Hazzd12/dissertation_2024/docs/asset/sensor_box.jpg

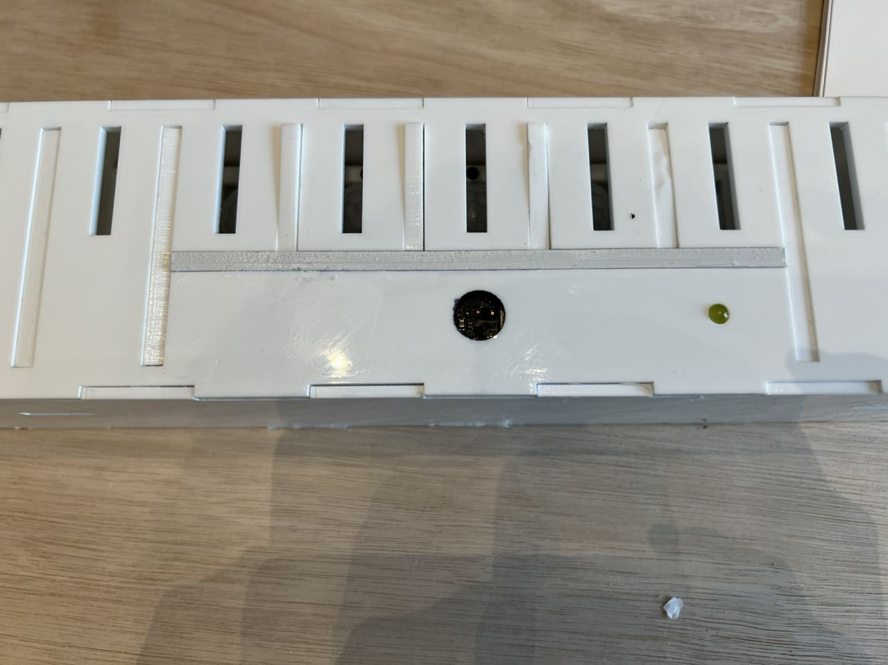
docs/asset/sensor_box.jpg
