Hazzd12/dissertation_2024/docs/asset/sensor_hole.jpg

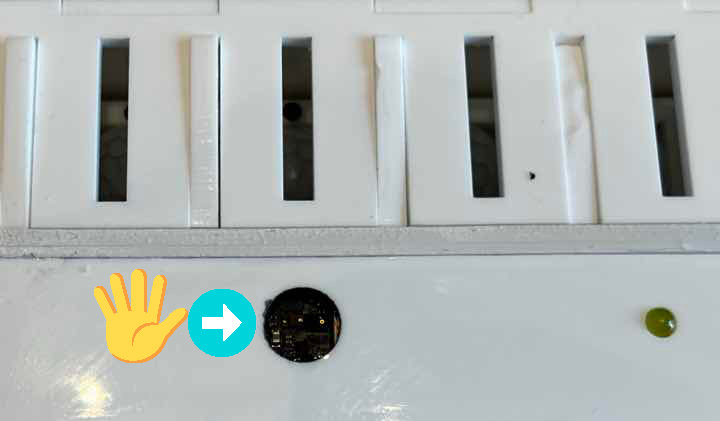
docs/asset/sensor_hole.jpg
