Hazzd12/dissertation_2024/dxf/sensor.png

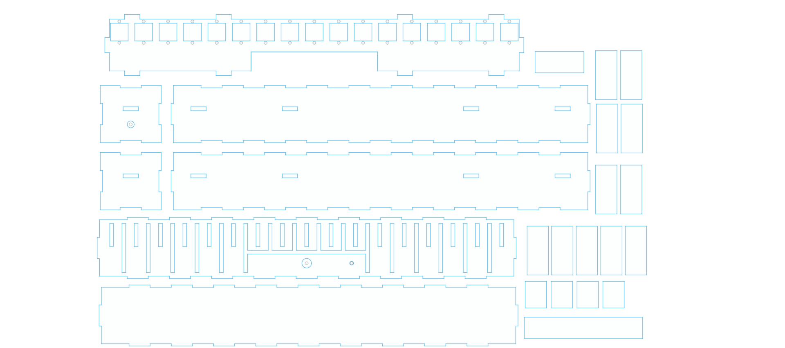
dxf/sensor.png
