Hazzd12/dissertation_2024/Arduino/leds/common.h

#ifndef __COMMON_H
#define __COMMON_H

typedef struct messageQue{
  char message[20];
  int yLocation;
} Mes;


const uint8_t font5x7[26][5] = {
    //  A-Z
    {0x1F, 0x28, 0x68, 0x28, 0x1F}, // A
    {0x7F, 0x49, 0x49, 0x49, 0x36}, // B
    {0x3E, 0x41, 0x41, 0x41, 0x41}, // C
    {0x7F, 0x41, 0x41, 0x22, 0x1C}, // D
    {0x7F, 0x49, 0x49, 0x49, 0x41}, // E
    {0x7F, 0x48, 0x48, 0x48, 0x40}, // F
    {0x3E, 0x41, 0x49, 0x49, 0x46}, // G
    {0x7F, 0x08, 0x08, 0x08, 0x7F}, // H
    {0x41, 0x41, 0x7F, 0x41, 0x41}, // I
    {0x46, 0x41, 0x41, 0x7E, 0x40}, // J
    {0x7F, 0x18, 0x24, 0x42, 0x01}, // K
    {0x7F, 0x01, 0x01, 0x01, 0x01}, // L
    {0x7F, 0x20, 0x1E, 0x20, 0x7F}, // M
    {0x7F, 0x20, 0x1C, 0x02, 0x7F}, // N
    {0x3E, 0x41, 0x41, 0x41, 0x3E}, // O
    {0x7F, 0x48, 0x48, 0x48, 0x30}, // P
    {0x3E, 0x41, 0x45, 0x43, 0x3F}, // Q
    {0x7F, 0x48, 0x4C, 0x4A, 0x31}, // R
    {0x31, 0x49, 0x49, 0x49, 0x46}, // S
    {0x40, 0x40, 0x7F, 0x40, 0x40}, // T
    {0x7E, 0x01, 0x01, 0x01, 0x7E}, // U
    {0x7C, 0x02, 0x01, 0x02, 0x7C}, // V
    {0x7F, 0x02, 0x1C, 0x02, 0x7F}, // W
    {0x63, 0x14, 0x08, 0x14, 0x63}, // X
    {0x60, 0x10, 0x0F, 0x10, 0x60}, // Y
    {0x43, 0x44, 0x49, 0x51, 0x61}, // Z
    
};

const uint8_t num3x7[10][3] ={
  {0x7F,0x41,0x7F}, //0
  {0x21,0x7F,0x01}, //1
  {0x4F,0x49,0x79}, //2
  {0x49,0x49,0x7F}, //3
  {0x78,0x08,0x7F}, //4
  {0x79,0x49,0x4F}, //5
  {0x7F,0x49,0x4F}, //6
  {0x40,0x40,0x7F}, //7
  {0x7F,0x49,0x7F}, //8
  {0x79,0x49,0x7F} //9
};

const uint8_t symbols1x7[2] = 
{
  0x01, //.
  0x11  //:
};

 //☁ X:4, Y:5
const uint16_t cloud[22]={   
  0x00E,
  0x01F,
  0x03F,
  0x07F,
  0x0FF,
  0x0FF,
  0x0FF,
  0x07F,
  0x07F,
  0x1FF,
  0x3FF,
  0x7FF,
  0x7FF,
  0x7FF,
  0x7FF,
  0x7FF,
  0x3FF,
  0x1FF,
  0x1FF,
  0x0FF,
  0x03F,
  0x01E
};

const uint8_t smallCloud[5]={
  0x03,0x07,0x0F,0x07,0x03
};

//X:6, Y:1 
const uint32_t sun[2][19] ={
  {
    0x00100,0x00100,0x08102,0x04004,
    0x02388,0x00FE0,0x01FF0,0x01FF0,
    0x03FF8,0x0BFFB,0x03FF8,0x01FF0,
    0x01FF0,0x00FE0,0x02388,0x04004,
    0x08102,0x00100,0x00100
  },
  {
    0x00000,0x01010,0x01830,0x00820,
    0x00380,0x18FE3,0x0DFF6,0x01FF0,
    0x03FF8,0x0BFFB,0x03FF8,0x01FF0,
    0x0DFF6,0x18FE3,0x00380,0x00820,
    0x01830,0x01010,0x00000
  }
};

const uint8_t thunder[5]={
  0x04,0x1A,0x2C,0x48,0x08
};


const uint16_t rSun[32] ={
  0x0003,0x000F,0x003F,0x00FF,
  0x01FF,0x03FF,0x07FF,0x0FFF,
  0x0FFF,0x1FFF,0x1FFF,0x3FFF,
  0x3FFF,0x7FFF,0x7FFF,0x7FFF,
  0x7FFF,0x7FFF,0x7FFF,0x3FFF,
  0x3FFF,0x1FFF,0x1FFF,0x0FFF,
  0x0FFF,0x07FF,0x03FF,0x01FF,
  0x00FF,0x003F,0x000F,0x0003
};

#endif
