Hazzd12/dissertation_2024/Arduino/leds/myWifi.h

// WiFi credentials
// #define WIFISSID "CE-Hub-Student"
// #define WIFIPASSWORD "casa-ce-gagarin-public-service"
#define WIFISSID "UCL_IoT"
#define WIFIPASSWORD "3JgttrTFLd"
#define MQTT_SERVER "mqtt.cetools.org"
#define MQTT_PORT 1884
#define MQTT_USER "student"
#define MQTT_PASS "ce2021-mqtt-forget-whale"
